wigman27/Arduino-Programmable-Constant-Current-Power-Resistance-Load/LTSpice/Spice Model - Version 3 - LM324.asc

C1: cap; 100n
C2: cap; 22n
C3: cap; 100n
C4: cap; 100n
C5: cap; 2.2µ
C6: cap; 100n
M2: nmos; BUK954R8-60E
R1: res; 0.1; tol=1
R2: res; 15k
R3: res; 10k
R4: res; 470
R5: res; 1k
R6: res; 10k
R7: res; 220k
R8: res; 10k
R10: res; 2.2
U3: opamp2; LM324
Vcc: voltage; 4.5
Vdac: voltage; 2
VLoad: voltage; 24
Named nets: 0, Vcc, VLoad, Vdac
.tran 100m
.inc BUK954R8-60E.lib
.inc lm324.txt
