wigman27/Arduino-Programmable-Constant-Current-Power-Resistance-Load/LTSpice/Auto Selector - Arduino.asc

D1: schottky; 1N5817
M1: pmos; BSS84
R1: res; 10k
R2: res; 10k
R10: res; 100
U1: LM358_NS
V1: voltage; 0
V2: voltage; 5
Named nets: 0, VIN, VUSB, VCC
.tran 10m
