wigman27/Arduino-Programmable-Constant-Current-Power-Resistance-Load/LTSpice/Auto Selector.asc

C1: cap; 10µ
C2: cap; 1µ
C3: cap; 10µ
C4: cap; 1µ
R1: res; 10k
R2: res; 1MEG
R3: res; 10k
R4: res; 1MEG
U1: FDN304p
U2: LM358_NS
U3: LM358_NS
U4: FDN304p
V1: voltage; 5
V2: voltage; 0
Named nets: 0, VIN, VCC, VUSB
FDN340P
FDN340P
