wigman27/Arduino-Programmable-Constant-Current-Power-Resistance-Load/LTSpice/Spice Model - Version 2.asc

C1: cap; 100n
C2: cap; 100n
C3: cap; 100n
M2: nmos; BUK954R8-60E
R1: res; 0.1; tol=1
R2: res; 10k
R3: res; 1.5k
R4: res; 100
R5: res; 1.5k
R6: res; 1k
U1: LT1014
V1: voltage; 12
V2: voltage; 24
V3: voltage; 4
V4: voltage; PULSE(0 5 0.5m 0 0 0.5m 1m)
Named nets: 0
.tran 10m
.inc BUK954R8-60E.lib
